NedelcuBogdanSebastian/SistemTreceri/Circuits/SenzorDPCutie/Top.png

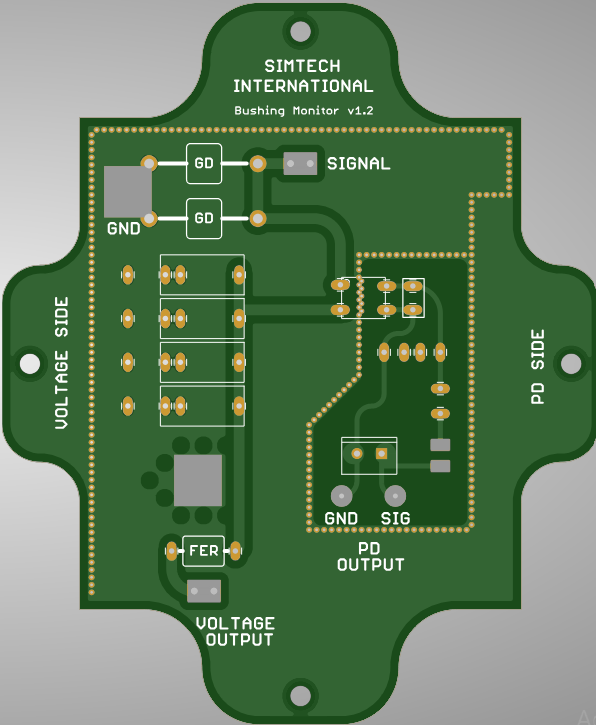
Circuits/SenzorDPCutie/Top.png
