NedelcuBogdanSebastian/SistemTreceri/Circuits/SwitchCanaleDP2024/Top.png

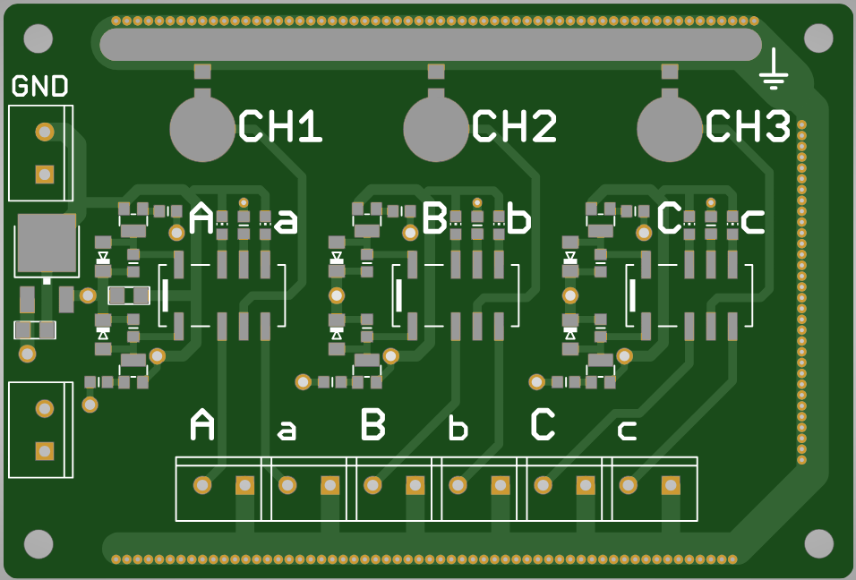
Circuits/SwitchCanaleDP2024/Top.png
