NedelcuBogdanSebastian/SistemTreceri/Circuits/ZIntermediar2023/Top.png

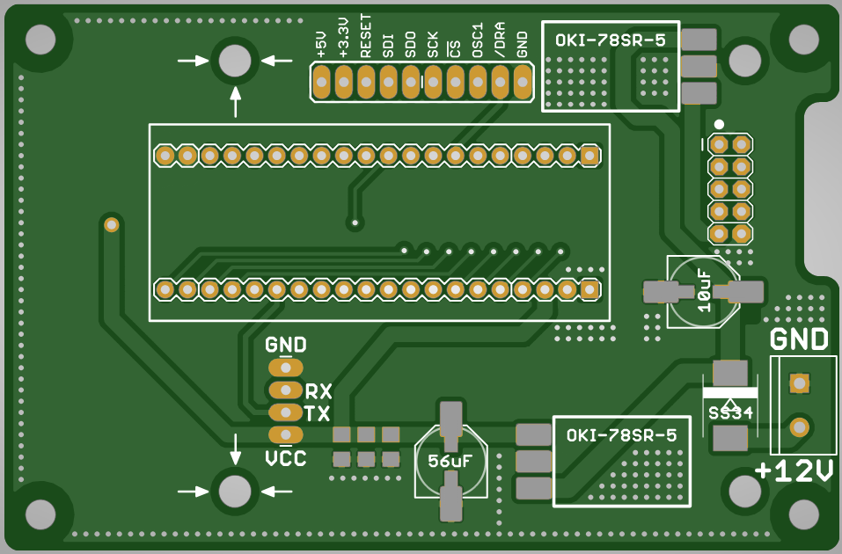
Circuits/ZIntermediar2023/Top.png
