NedelcuBogdanSebastian/SistemTreceri/Circuits/ZIntermediar2024/Top.png

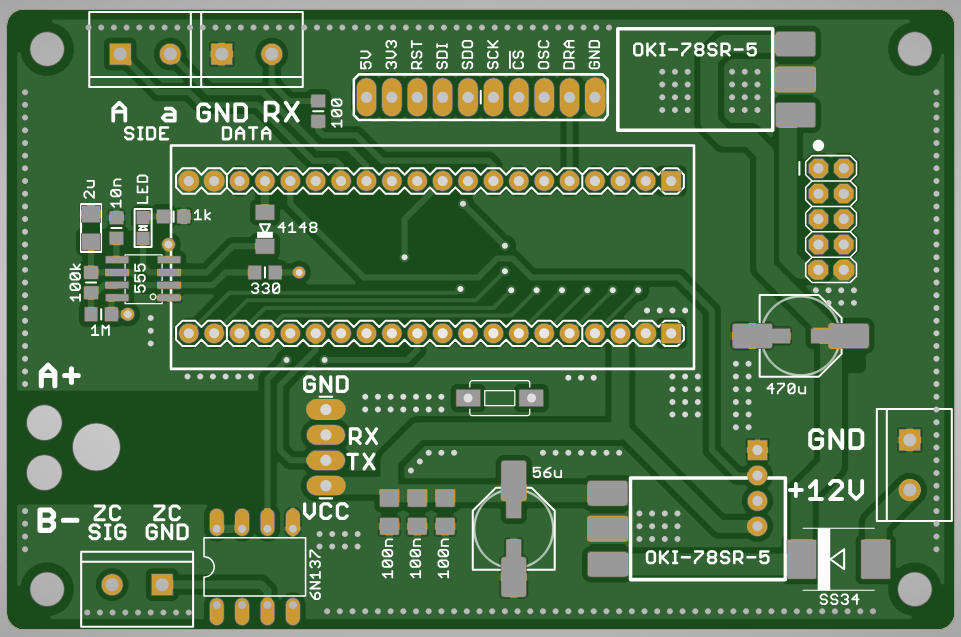
Circuits/ZIntermediar2024/Top.png
