NedelcuBogdanSebastian/SistemTreceri/Circuits/Zaq_HAND_SOLDERING/Top.png

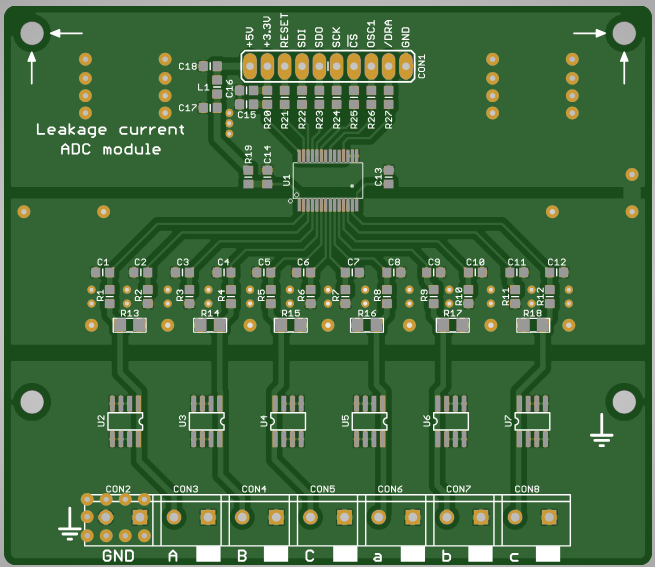
Circuits/Zaq_HAND_SOLDERING/Top.png
