NedelcuBogdanSebastian/SistemTreceri/Circuits/CT_Adapter/CT_Adapter_MOD4ELECROW.brd

## EAGLE design Circuits/CT_Adapter/CT_Adapter_MOD4ELECROW.brd (2024-10-08)

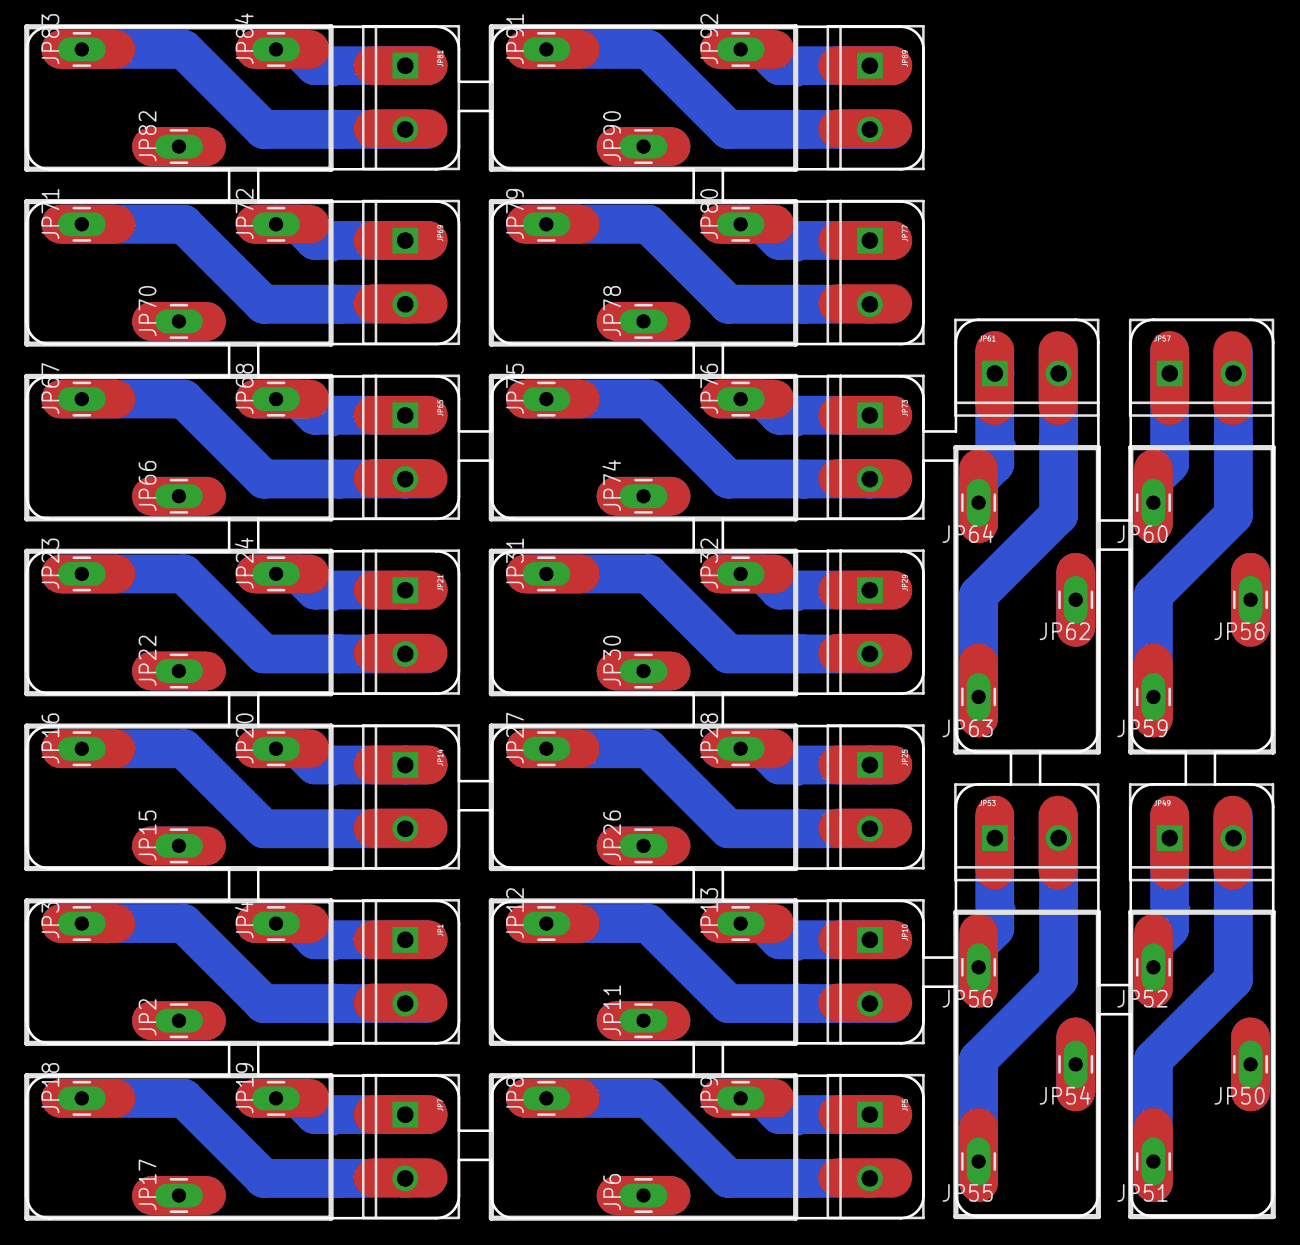
[picture p42: board CT_Adapter_MOD4ELECROW.brd from above]

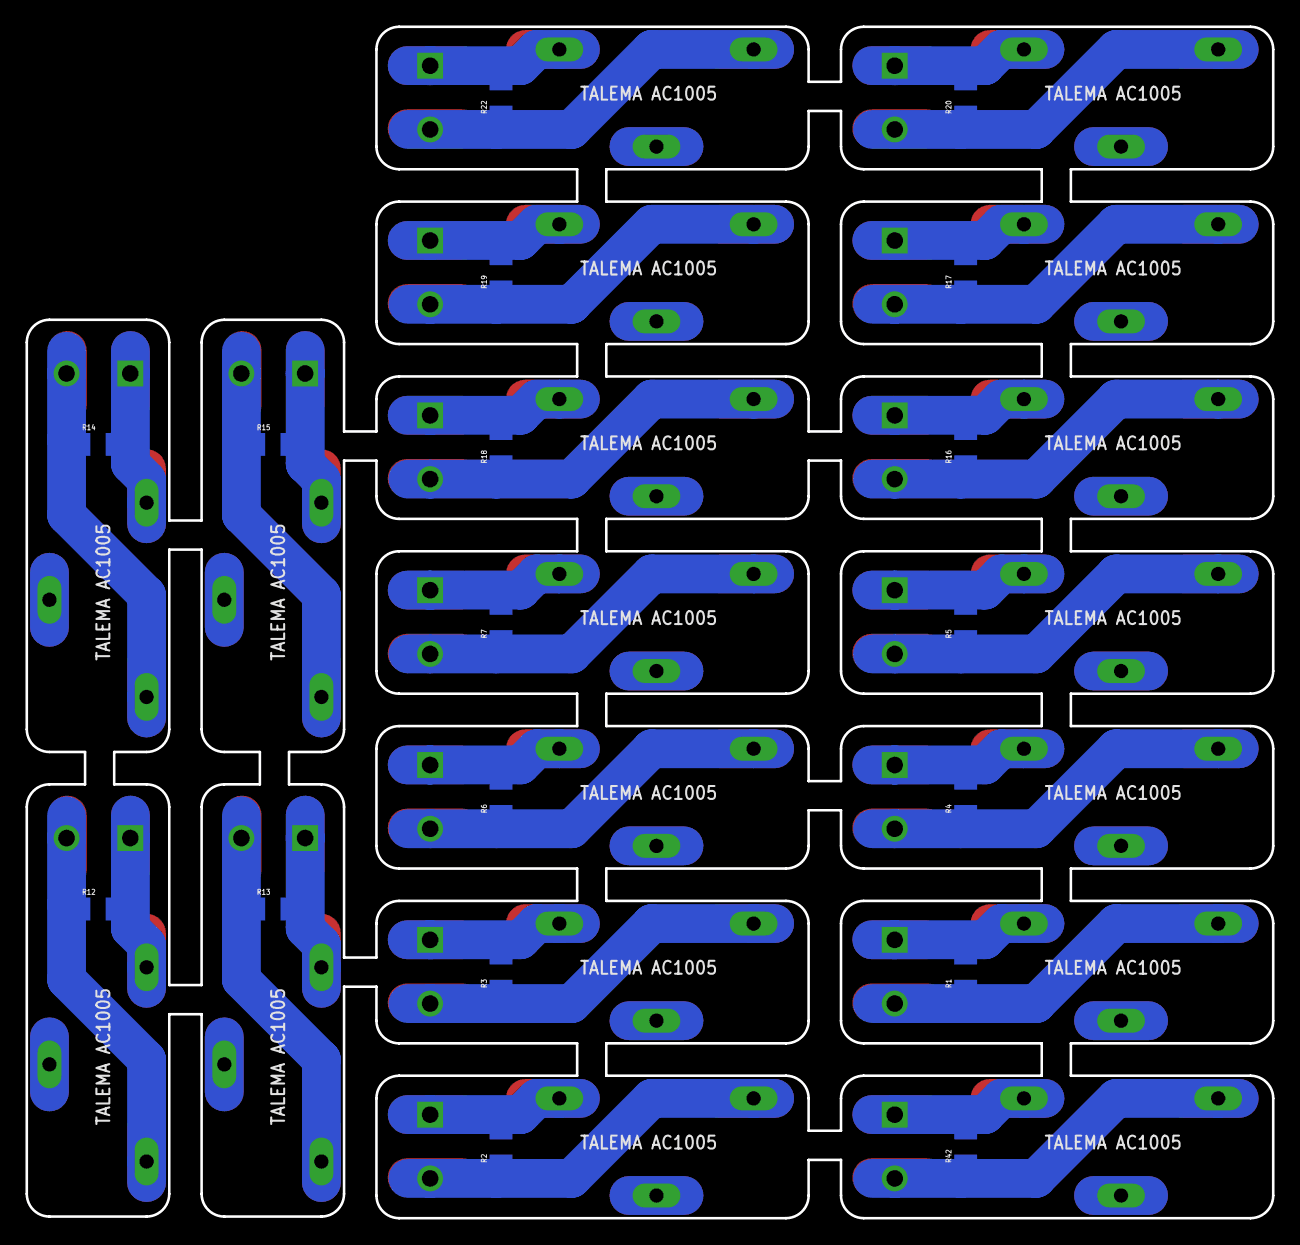
[picture p43: board CT_Adapter_MOD4ELECROW.brd from below]

Board: 2 copper layers, 97.8 x 93.5 mm, 90 parts (18 on the bottom side), 36 nets.

Parts:
JP1, JP5, JP7, JP10, JP14, JP21, JP25, JP29, JP49, JP53, JP57, JP61, JP65, JP69, JP73, JP77, JP81, JP89: SCREWTERMINAL-5MM-2
JP2, JP3, JP4, JP6, JP8, JP9, JP11, JP12, JP13, JP15, JP16, JP17, JP18, JP19, JP20, JP22, JP23, JP24, JP26, JP27, JP28, JP30, JP31, JP32, JP50, JP51, JP52, JP54, JP55, JP56, JP58, JP59, JP60, JP62, JP63, JP64, JP66, JP67, JP68, JP70, JP71, JP72, JP74, JP75, JP76, JP78, JP79, JP80, JP82, JP83, JP84, JP90, JP91, JP92: 1X01_LONGPAD
R1, R2, R3, R4, R5, R6, R7, R12, R13, R14, R15, R16, R17, R18, R19, R20, R22, R42: 50ohm; 1206

Connections:
AGND: JP7.1, JP19.1, R42.2
AGND1: JP1.1, JP4.1, R1.2
AGND2: JP5.1, JP9.1, R2.2
AGND3: JP10.1, JP13.1, R3.2
AGND4: JP14.1, JP20.1, R4.2
AGND5: JP21.1, JP24.1, R5.2
AGND6: JP25.1, JP28.1, R6.2
AGND7: JP29.1, JP32.1, R7.2
AGND12: JP49.1, JP52.1, R12.2
AGND13: JP53.1, JP56.1, R13.2
AGND14: JP57.1, JP60.1, R14.2
AGND15: JP61.1, JP64.1, R15.2
AGND16: JP65.1, JP68.1, R16.2
AGND17: JP69.1, JP72.1, R17.2
AGND18: JP73.1, JP76.1, R18.2
AGND19: JP77.1, JP80.1, R19.2
AGND20: JP81.1, JP84.1, R20.2
AGND22: JP89.1, JP92.1, R22.2
unnamed: JP7.2, JP18.1, R42.1
unnamed: JP1.2, JP3.1, R1.1
unnamed: JP5.2, JP8.1, R2.1
unnamed: JP10.2, JP12.1, R3.1
unnamed: JP14.2, JP16.1, R4.1
unnamed: JP21.2, JP23.1, R5.1
unnamed: JP25.2, JP27.1, R6.1
unnamed: JP29.2, JP31.1, R7.1
unnamed: JP49.2, JP51.1, R12.1
unnamed: JP53.2, JP55.1, R13.1
unnamed: JP57.2, JP59.1, R14.1
unnamed: JP61.2, JP63.1, R15.1
unnamed: JP65.2, JP67.1, R16.1
unnamed: JP69.2, JP71.1, R17.1
unnamed: JP73.2, JP75.1, R18.1
unnamed: JP77.2, JP79.1, R19.1
unnamed: JP81.2, JP83.1, R20.1
unnamed: JP89.2, JP91.1, R22.1
