NedelcuBogdanSebastian/SistemTreceri/treceri/main.h

/* Includes ------------------------------------------------------------------*/
#include "stm32f10x.h"


//extern u16 usRegInputBuf[100+1];
extern u16 usRegHoldingBuf[40+1];
extern u8 usRegCoilBuf[64/8+1];    // We have 64 coils
